denisagiuglan24/Proiect-TSC/Images/Screenshot 2026-04-22 121204.png

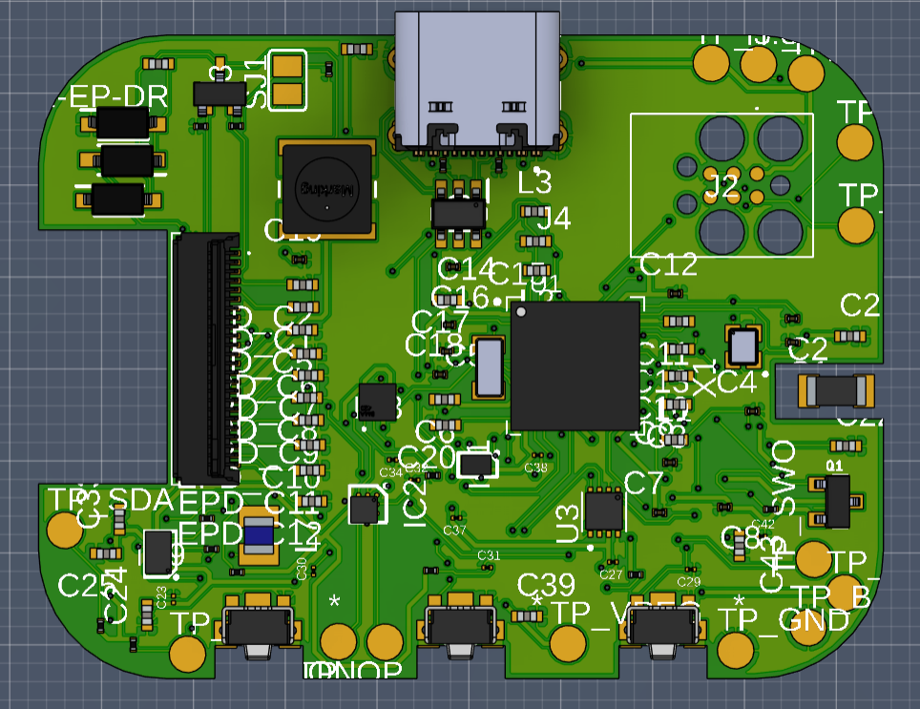
Images/Screenshot 2026-04-22 121204.png
