denisagiuglan24/Proiect-TSC/Images/Screenshot 2026-04-22 121425.png

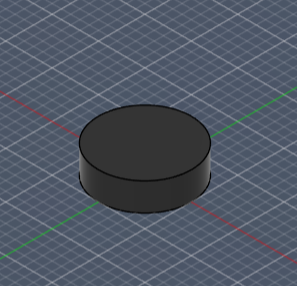
Images/Screenshot 2026-04-22 121425.png
